MoesGit/Motivation_Buddy/Software/Motivation_Buddy_V3/heart_map.h

const unsigned char heart_map [] PROGMEM = {
	// 'heart-clipart-black-and-white-images-free-download, 128x64px
	0xff, 0xff, 0xff, 0xff, 0xff, 0xf0, 0x07, 0xff, 0xff, 0xe0, 0x0f, 0xff, 0xff, 0xff, 0xff, 0xff, 
	0xff, 0xff, 0xff, 0xff, 0xff, 0x80, 0x00, 0xff, 0xff, 0x00, 0x01, 0xff, 0xff, 0xff, 0xff, 0xff, 
	0xff, 0xff, 0xff, 0xff, 0xfe, 0x00, 0x00, 0x3f, 0xfc, 0x00, 0x00, 0x7f, 0xff, 0xff, 0xff, 0xff, 
	0xff, 0xff, 0xff, 0xff, 0xf8, 0x0f, 0xf8, 0x1f, 0xf8, 0x1f, 0xf8, 0x1f, 0xff, 0xff, 0xff, 0xff, 
	0xff, 0xff, 0xff, 0xff, 0xf0, 0x7f, 0xfe, 0x0f, 0xf0, 0x7f, 0xfe, 0x0f, 0xff, 0xff, 0xff, 0xff, 
	0xff, 0xff, 0xff, 0xff, 0xe1, 0xff, 0xff, 0x83, 0xc1, 0xff, 0xff, 0x87, 0xff, 0xff, 0xff, 0xff, 
	0xff, 0xff, 0xff, 0xff, 0xc3, 0xff, 0xff, 0xe1, 0xc7, 0xff, 0xff, 0xc3, 0xff, 0xff, 0xff, 0xff, 
	0xff, 0xff, 0xff, 0xff, 0x87, 0xff, 0xff, 0xf1, 0x8f, 0xff, 0xff, 0xe1, 0xff, 0xff, 0xff, 0xff, 
	0xff, 0xff, 0xff, 0xff, 0x8f, 0xff, 0xff, 0xf8, 0x1f, 0xff, 0xff, 0xf0, 0xff, 0xff, 0xff, 0xff, 
	0xff, 0xff, 0xff, 0xff, 0x1f, 0xff, 0xff, 0xf8, 0x1f, 0xff, 0xff, 0xf8, 0xff, 0xff, 0xff, 0xff, 
	0xff, 0xff, 0xff, 0xfe, 0x1f, 0xff, 0xff, 0xfc, 0x3f, 0xff, 0xff, 0xfc, 0x7f, 0xff, 0xff, 0xff, 
	0xff, 0xff, 0xff, 0xfe, 0x3f, 0xff, 0xff, 0xfe, 0x7f, 0xff, 0xff, 0xfc, 0x7f, 0xff, 0xff, 0xff, 
	0xff, 0xff, 0xff, 0xfe, 0x7f, 0xff, 0xff, 0xfe, 0x7f, 0xff, 0xff, 0xfe, 0x7f, 0xff, 0xff, 0xff, 
	0xff, 0xff, 0xff, 0xfc, 0x7f, 0xff, 0xff, 0xff, 0xff, 0xff, 0xff, 0xfe, 0x3f, 0xff, 0xff, 0xff, 
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
	0xff, 0xff, 0xff, 0xff, 0xfc, 0x3f, 0xff, 0xff, 0xff, 0xff, 0xfc, 0x7f, 0xff, 0xff, 0xff, 0xff, 
	0xff, 0xff, 0xff, 0xff, 0xfe, 0x1f, 0xff, 0xff, 0xff, 0xff, 0xf8, 0xff, 0xff, 0xff, 0xff, 0xff, 
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
};
