MoesGit/Motivation_Buddy/Software/Motivation_Buddy_V3/settings.h

//Things to change
const char * ssid = "XXXXX";        //Change to your "wifi-name"
const char * password = "XXXXX";  //Change to your Passsword
String GOOGLE_SCRIPT_ID = "XXXXX";  //Change to Script ID 
